dualvim/ESP32CAM_ESPNOW_Sensors_WebServer/Images/P_20200203_075402.jpg

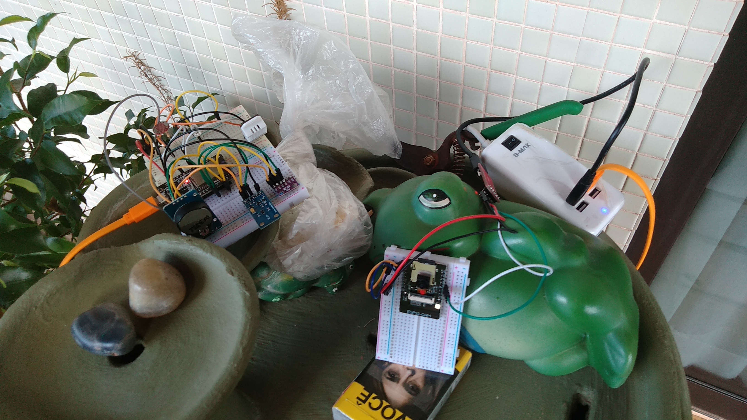
Images/P_20200203_075402.jpg
