dualvim/ESP32CAM_ESPNOW_Sensors_WebServer/Images/P_20200203_075407.jpg

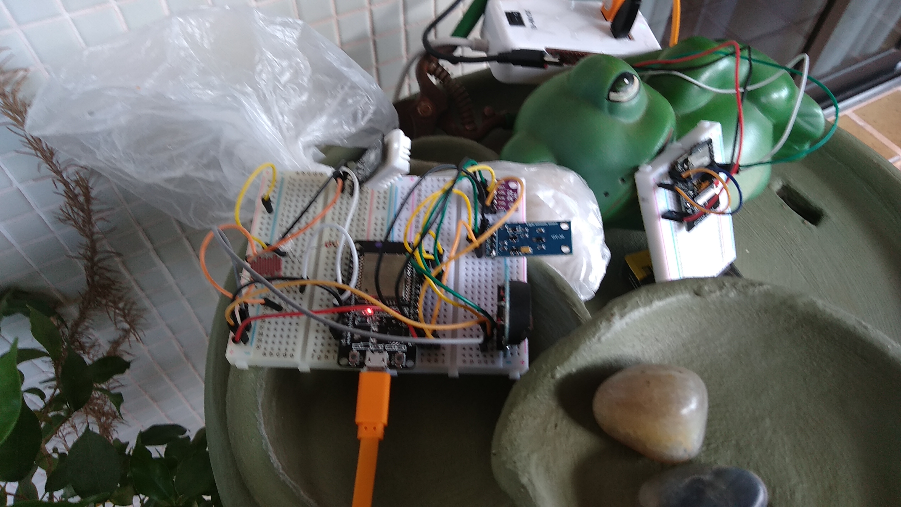
Images/P_20200203_075407.jpg
