dualvim/ESP32CAM_ESPNOW_Sensors_WebServer/Images/P_20200203_085529.jpg

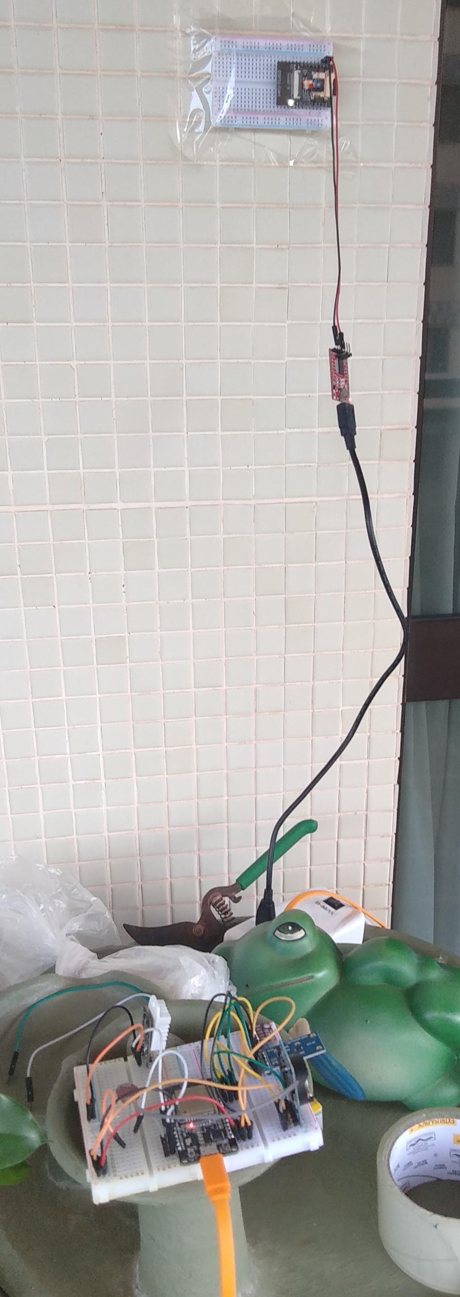
Images/P_20200203_085529.jpg
